edwards414/pcb_project/picture/3d模擬.PNG

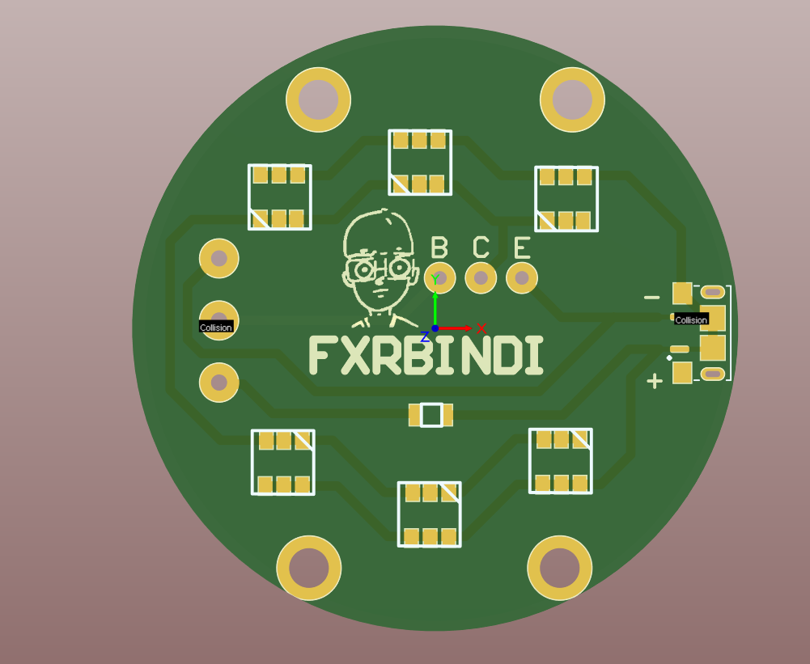
picture/3d模擬.PNG
