edwards414/pcb_project/picture/3d模擬背面.PNG

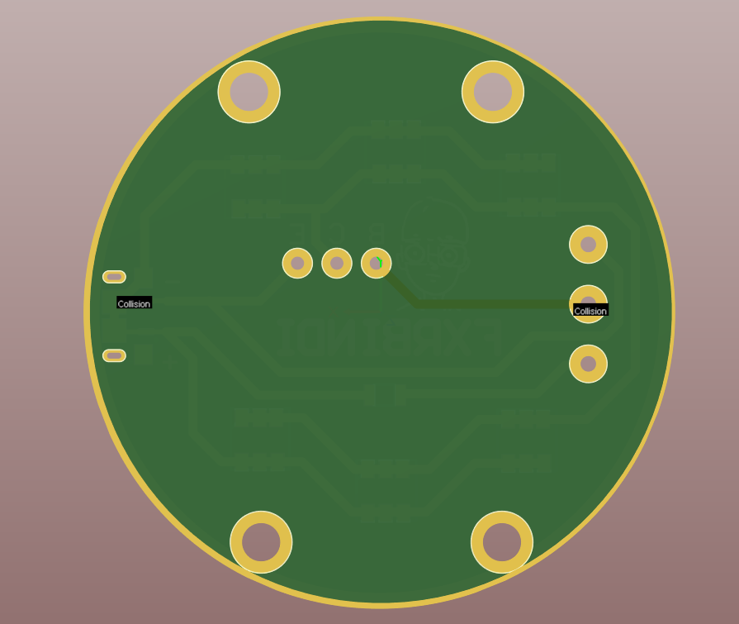
picture/3d模擬背面.PNG
