edwards414/pcb_project/picture/flatcam1.PNG

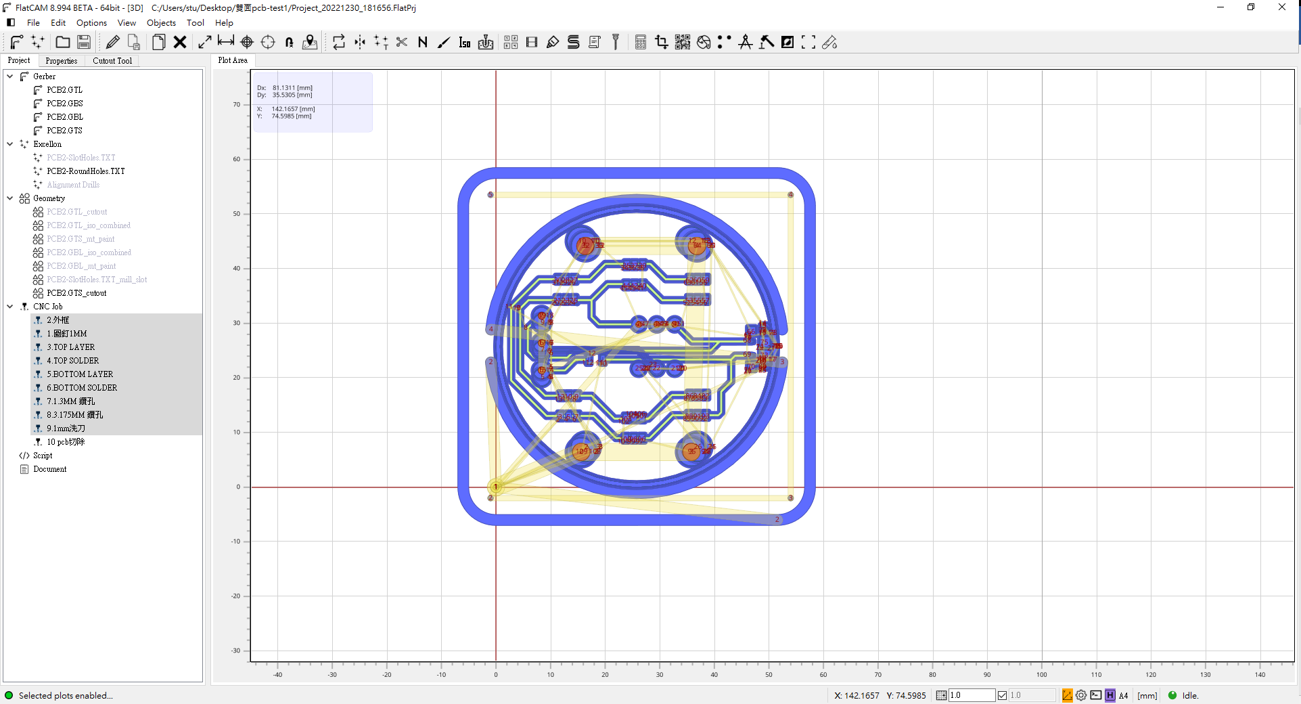
picture/flatcam1.PNG
