edwards414/pcb_project/picture/FLATCAM.PNG

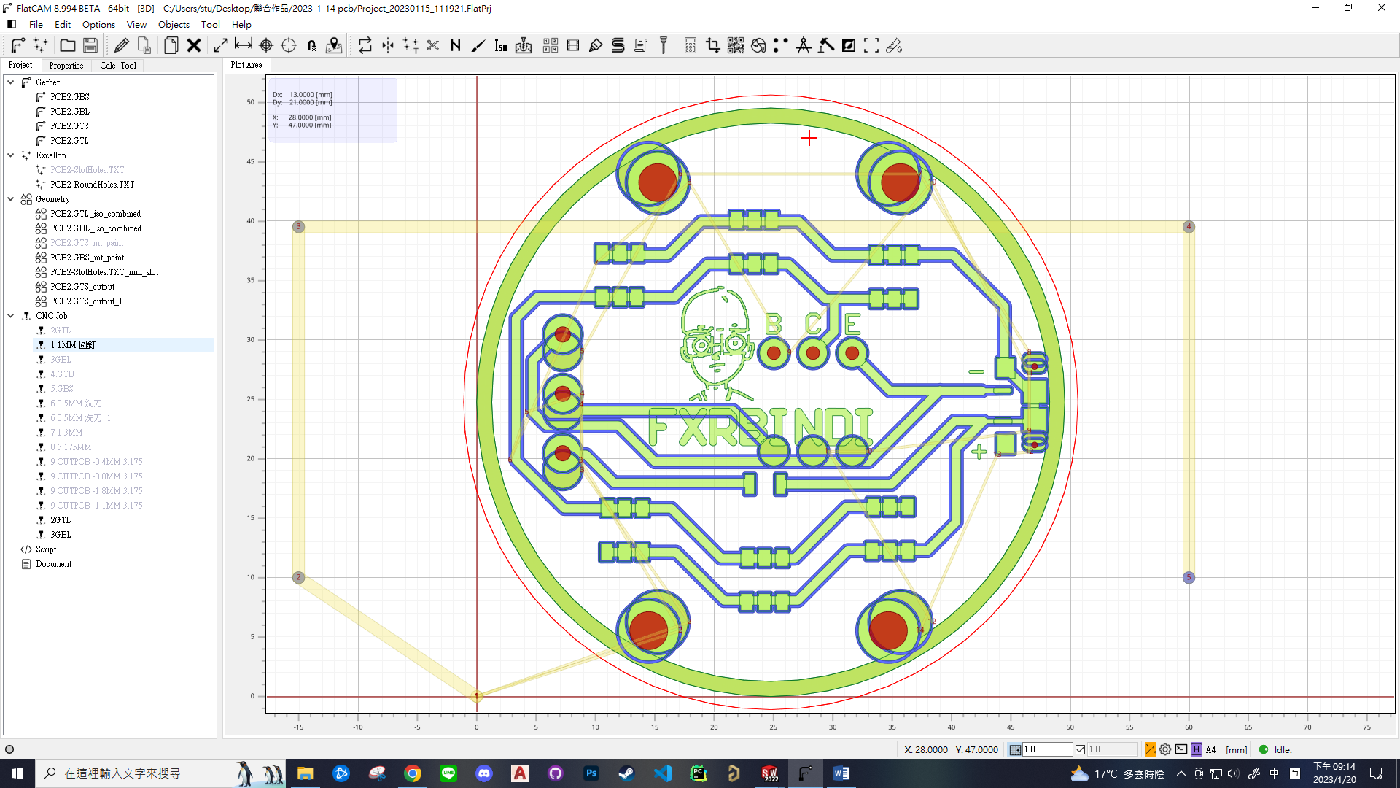
picture/FLATCAM.PNG
