edwards414/pcb_project/picture/PCB 3D.PNG

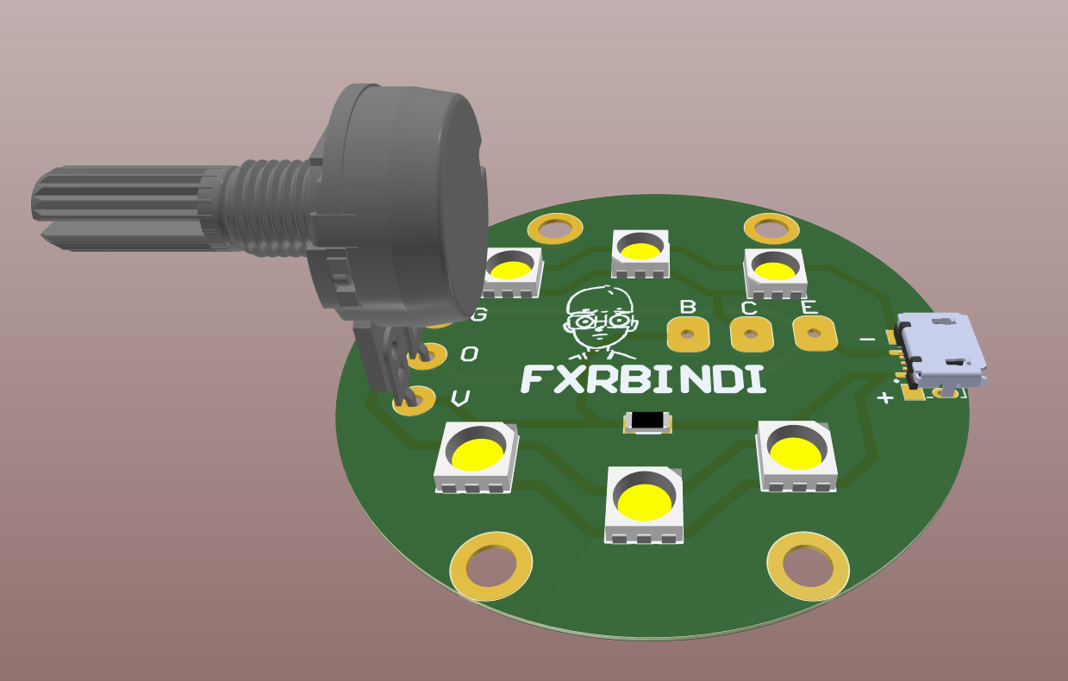
picture/PCB 3D.PNG
