edwards414/pcb_project/picture/上蓋.PNG

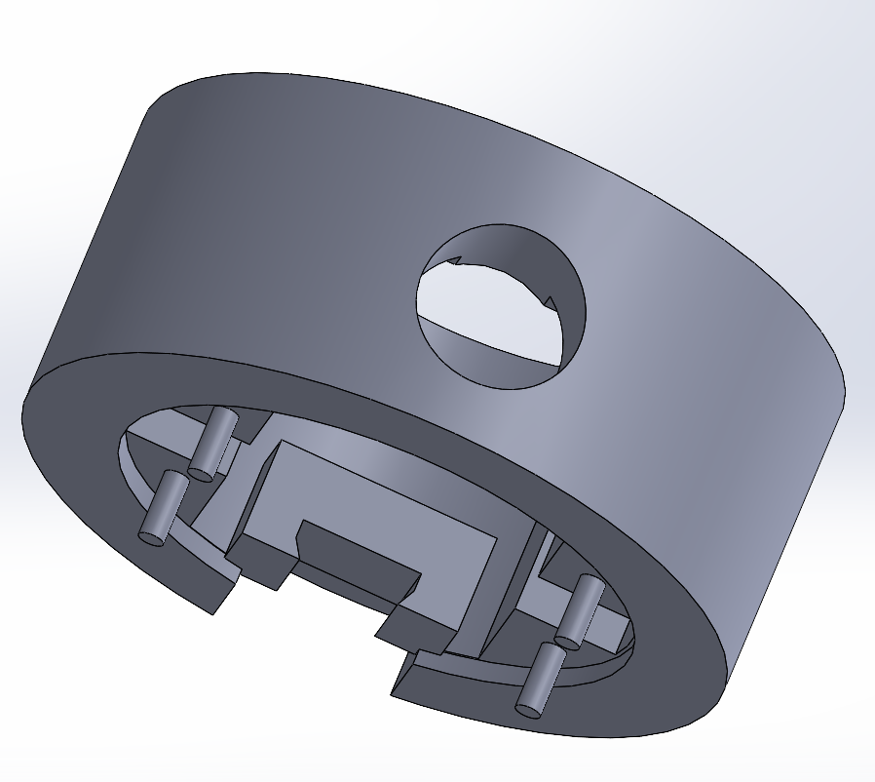
picture/上蓋.PNG
