edwards414/pcb_project/picture/下座.PNG

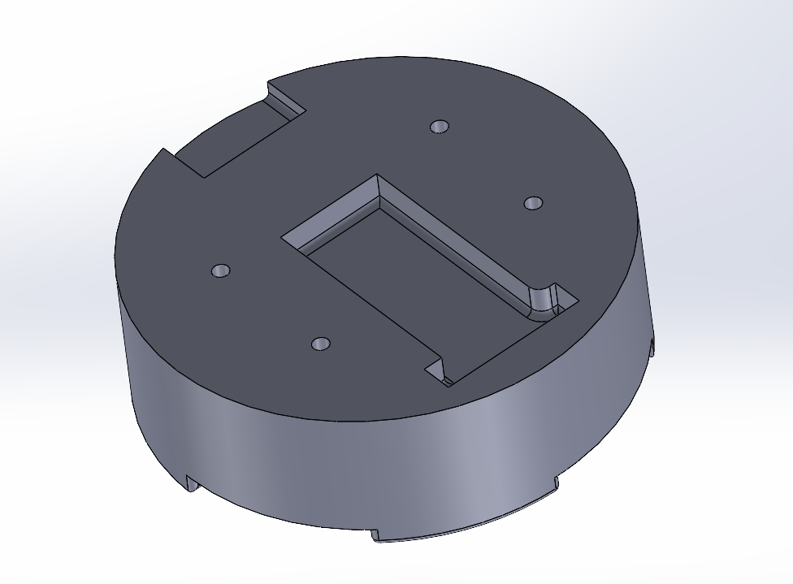
picture/下座.PNG
