edwards414/pcb_project/picture/問題一.PNG

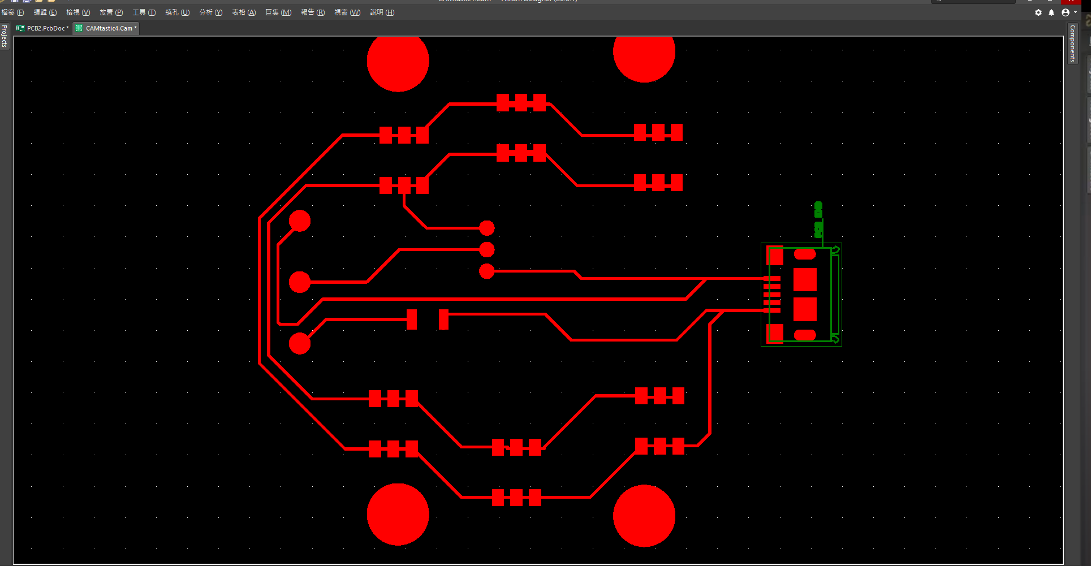
picture/問題一.PNG
