edwards414/pcb_project/picture/擷取.PNG

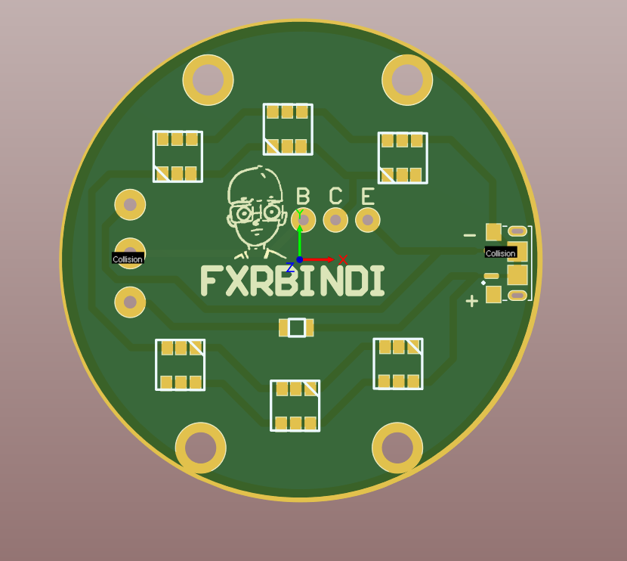
picture/擷取.PNG
